cesarandreu/laser_tag_reloaded/include/WireBaseL.h

/******************************************************************************
 * The MIT License
 *
 * Copyright (c) 2010 LeafLabs LLC.
 *
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
 * THE SOFTWARE IS PROVIDED "AS IS", WITHOUT WARRANTY OF ANY KIND,
 * EXPRESS OR IMPLIED, INCLUDING BUT NOT LIMITED TO THE WARRANTIES OF
 * MERCHANTABILITY, FITNESS FOR A PARTICULAR PURPOSE AND
 * NONINFRINGEMENT. IN NO EVENT SHALL THE AUTHORS OR COPYRIGHT HOLDERS
 * BE LIABLE FOR ANY CLAIM, DAMAGES OR OTHER LIABILITY, WHETHER IN AN
 * ACTION OF CONTRACT, TORT OR OTHERWISE, ARISING FROM, OUT OF OR IN
 * CONNECTION WITH THE SOFTWARE OR THE USE OR OTHER DEALINGS IN THE
 * SOFTWARE.
 *****************************************************************************/

/**
 * @file WireBaseL.h
 * @author Trystan Jones <crenn6977@gmail.com>
 * @brief Wire library, following the majority of the interface from Arduino.
 *        Provides a 'standard' interface to I2C (two-wire) communication for
 *        derived classes.
 */

/*
 * Library created by crenn to allow a system which would provide users
 * a method for interfacing with I2C devices regardless of
 * whether it is I2C hardware or emulating software.
 */

#ifndef _WIREBASEL_H_
#define _WIREBASEL_H_

/* Conditional extern "C" so we're safe to call from C++ files */
#ifdef __cplusplus
extern "C" {
#endif

#include <libmaple/i2c.h>
#include <libmaple/libmaple_types.h>

#define WIRE_BUFSIZ 32

/* return codes from endTransmission() */
#define SUCCESS   0        /* transmission was successful */
#define EDATA     1        /* too much data */
#define ENACKADDR 2        /* received nack on transmit of address */
#define ENACKTRNS 3        /* received nack on transmit of data */
#define EOTHER    4        /* other error */

//Type definitions
typedef uint8 boolean;
typedef uint8 byte;

i2c_msg itc_msg;
uint8 rx_buf[WIRE_BUFSIZ];      /* receive buffer */
uint8 rx_buf_idx;               /* first unread idx in rx_buf */
uint8 rx_buf_len;               /* number of bytes read */

uint8 tx_buf[WIRE_BUFSIZ];      /* transmit buffer */
uint8 tx_buf_idx;  // next idx available in tx_buf, -1 overflow
boolean tx_buf_overflow;

/*
 * Initialises the I2C interface
 */
void i2c_begin();

/*
 * Sets up the transmission message to be processed
 */
void i2c_beginTransmission(uint8 slave_address);

/*
 * Allow only 8 bit addresses to be used
 */
void i2c_beginTransmissionInt(int slave_address);

/*
 * Call the process function to process the message if the TX
 * buffer has not overflowed.
 */
uint8 i2c_endTransmission(void);

/*
 * Request bytes from a slave device and process the request,
 * storing into the receiving buffer.
 */
uint8 i2c_requestFrom(uint8 address, int num_bytes);

/*
 * Allow only 8 bit addresses to be used when requesting bytes
 */
uint8 i2c_requestFromInt(int address, int numBytes);

/*
 * Stack up bytes to be sent when transmitting
 */
void i2c_send(uint8 value);

/*
 * Stack up bytes from the array to be sent when transmitting
 */
void i2c_sendArr(uint8* buf, int len);

/*
 * Ensure that a sending data will only be 8-bit bytes
 */
void i2c_sendInt(int value);

/*
 * Ensure that an array sending data will only be 8-bit bytes
 */
void i2c_sendIntArr(int* buf, int len);

/*
 * Stack up bytes from a string to be sent when transmitting
 */
void i2c_sendString(char* buf);

/*
 * Return the amount of bytes that is currently in the receiving buffer
 */
uint8 i2c_available();

/*
 * Return the value of byte in the receiving buffer that is currently being
 * pointed to
 */
uint8 i2c_receive();

#ifdef __cplusplus
}
#endif

#endif // _WIREBASEL_H_
